louis-bourgault/macondo-games/art/flappy-bg.png

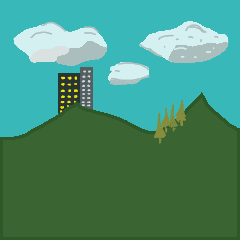
art/flappy-bg.png
