louis-bourgault/macondo-games/img/fusion-with-parts.png

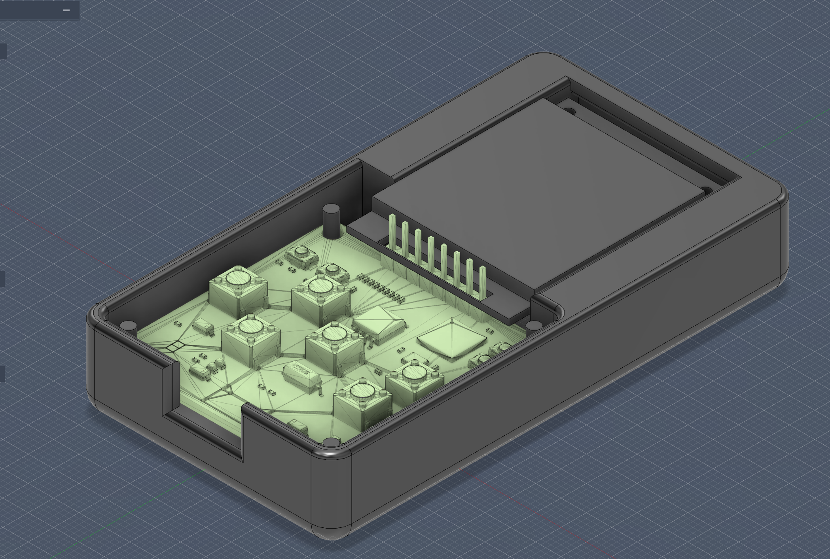
img/fusion-with-parts.png
