louis-bourgault/macondo-games/img/instructions.jpg

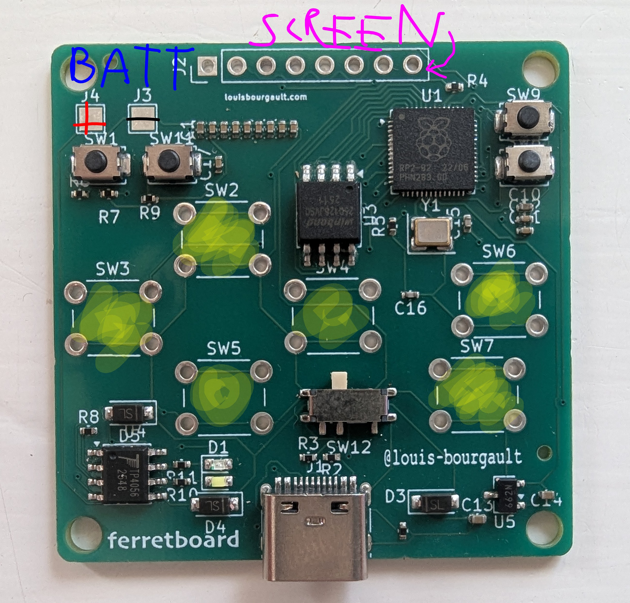
img/instructions.jpg
