louis-bourgault/macondo-games/img/screensolder.jpg

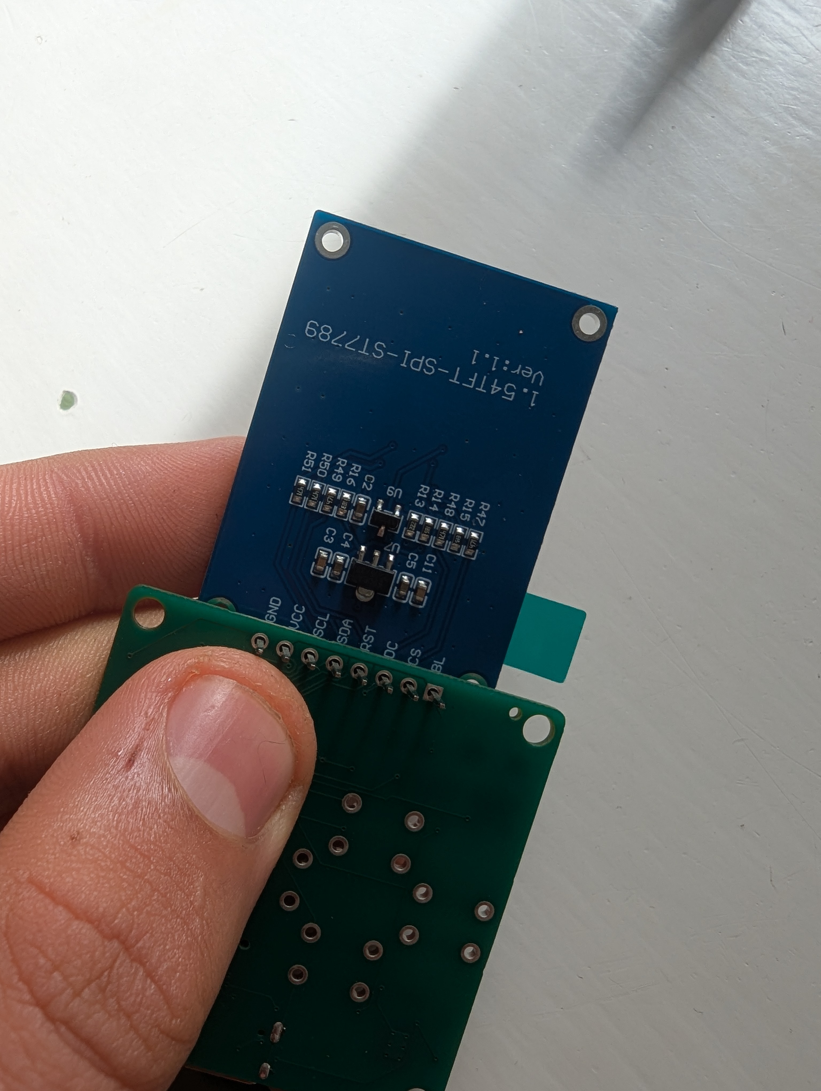
img/screensolder.jpg
